Andrew702/4-DOF-Pick-Place-Robot/screen shots/end_scopeout.PNG

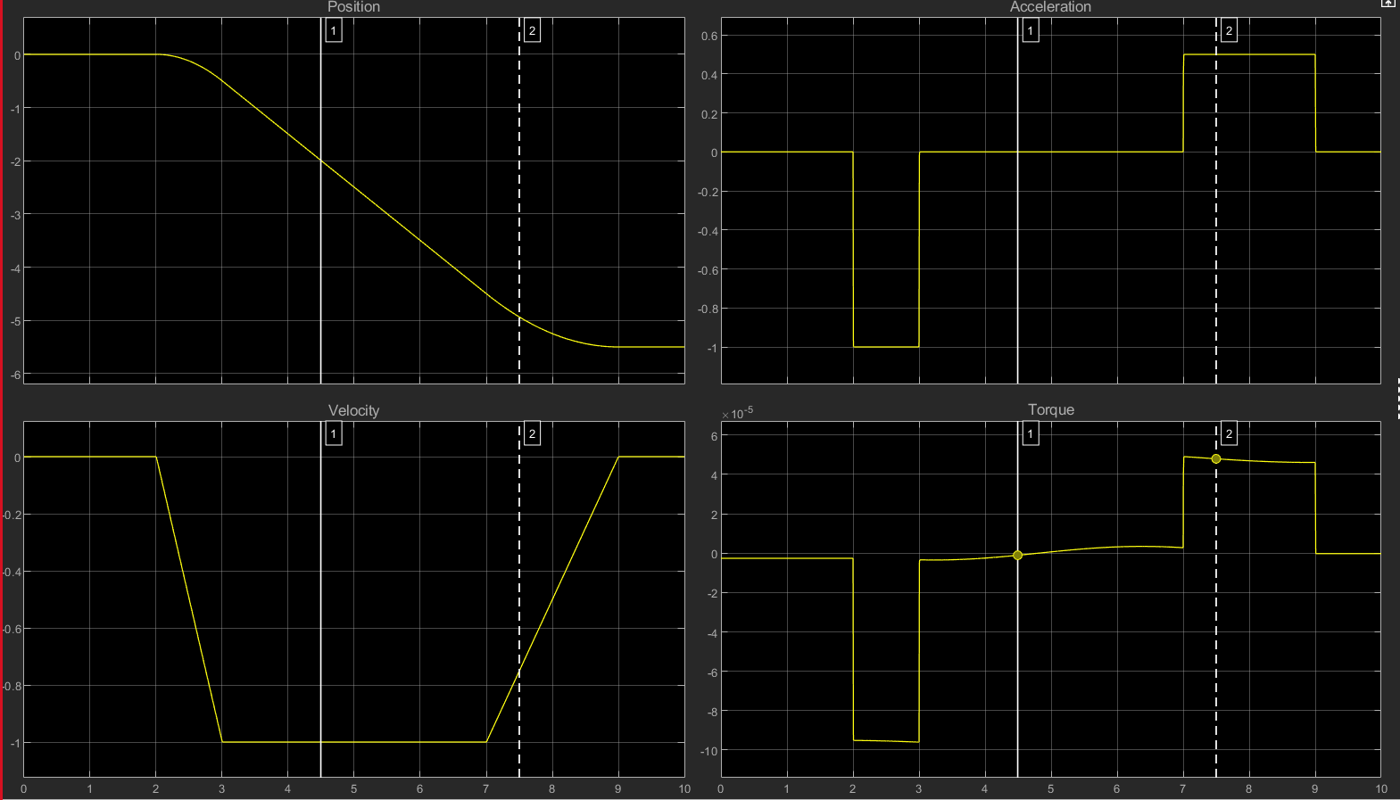
screen shots/end_scopeout.PNG
