Andrew702/4-DOF-Pick-Place-Robot/screen shots/end_torque.PNG

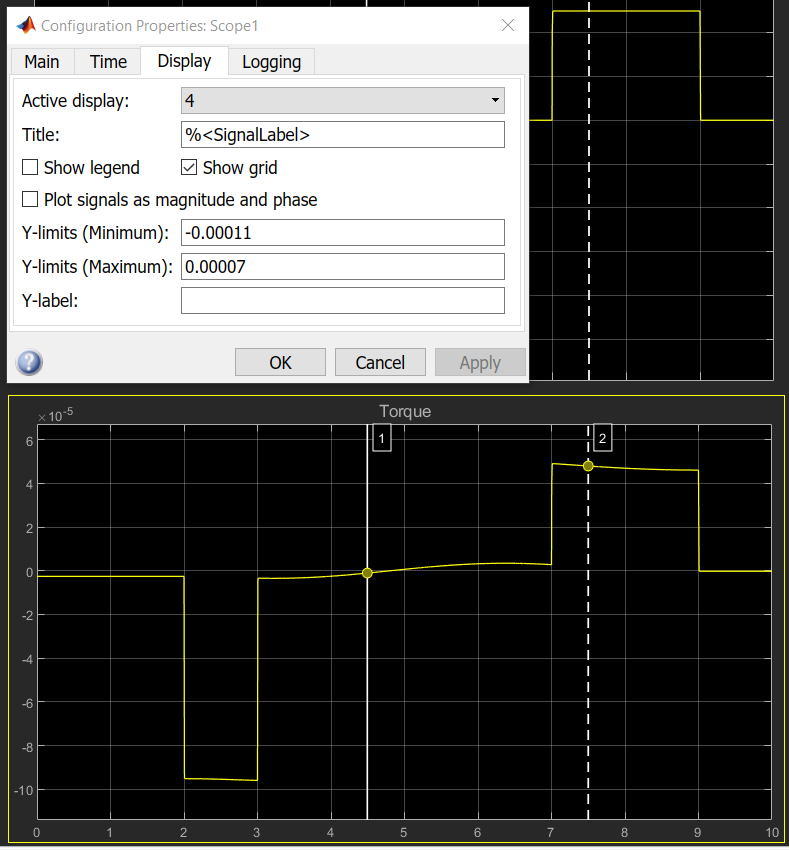
screen shots/end_torque.PNG
