Andrew702/4-DOF-Pick-Place-Robot/screen shots/hm_torque.PNG

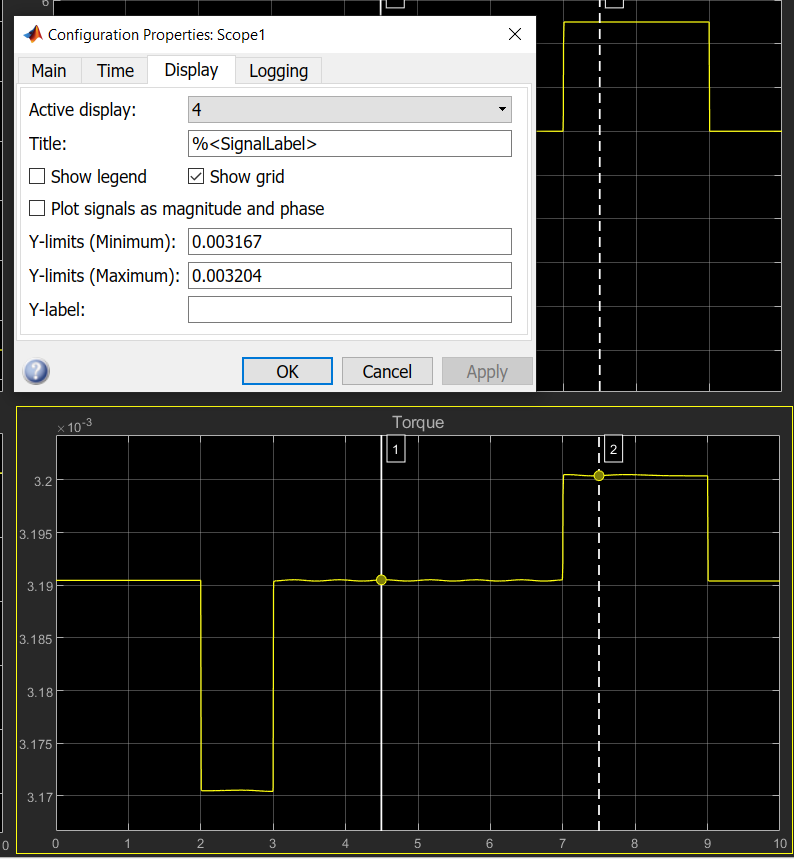
screen shots/hm_torque.PNG
