Andrew702/4-DOF-Pick-Place-Robot/screen shots/pid0.1.PNG

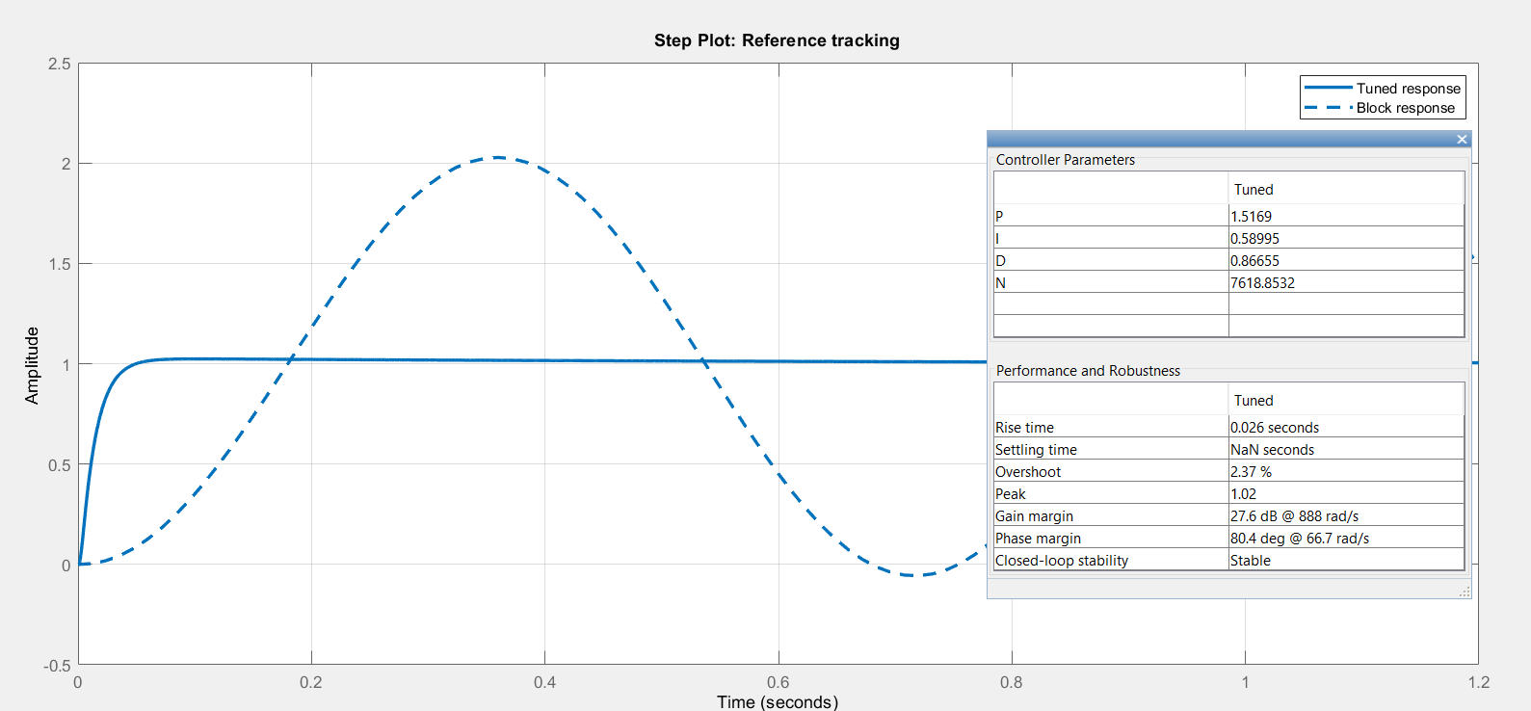
screen shots/pid0.1.PNG
