Andrew702/4-DOF-Pick-Place-Robot/screen shots/pid0.2.PNG

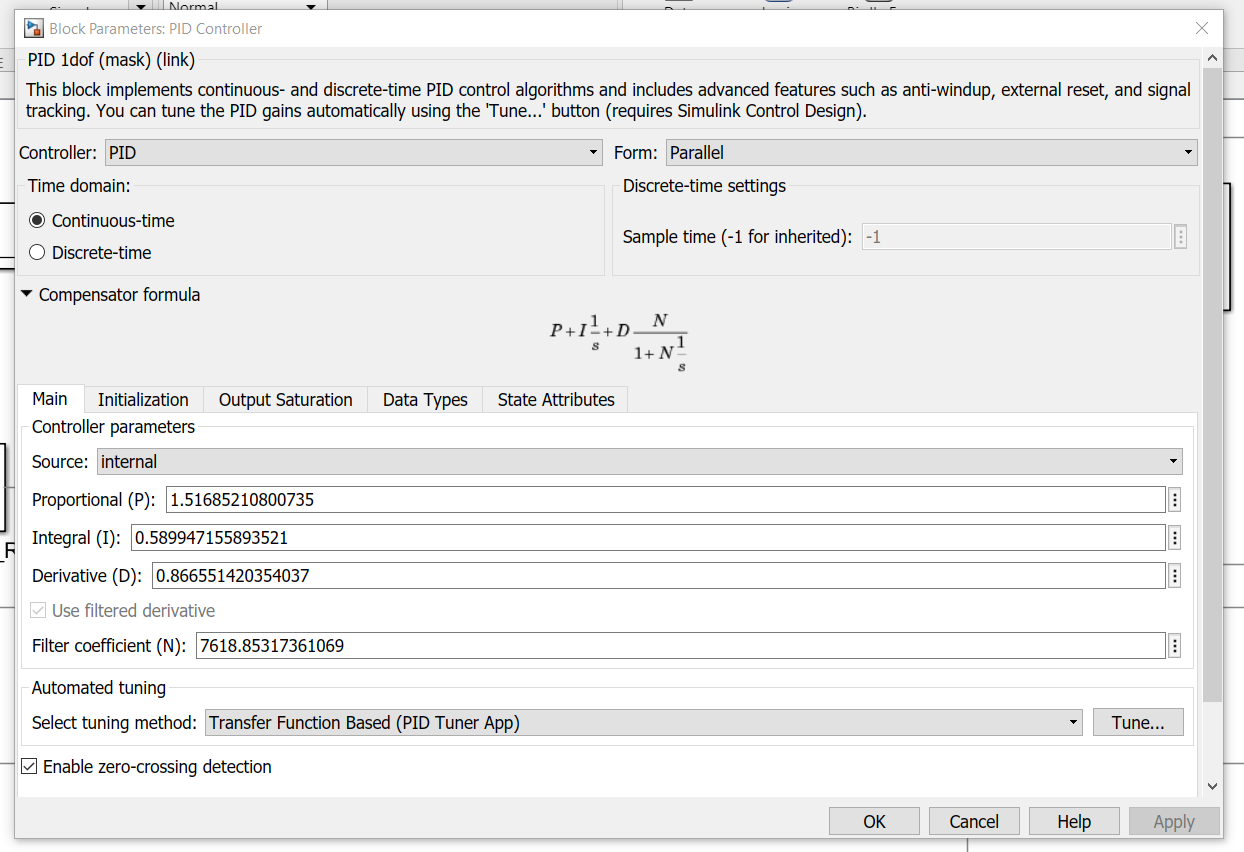
screen shots/pid0.2.PNG
