Andrew702/4-DOF-Pick-Place-Robot/screen shots/pid final.PNG

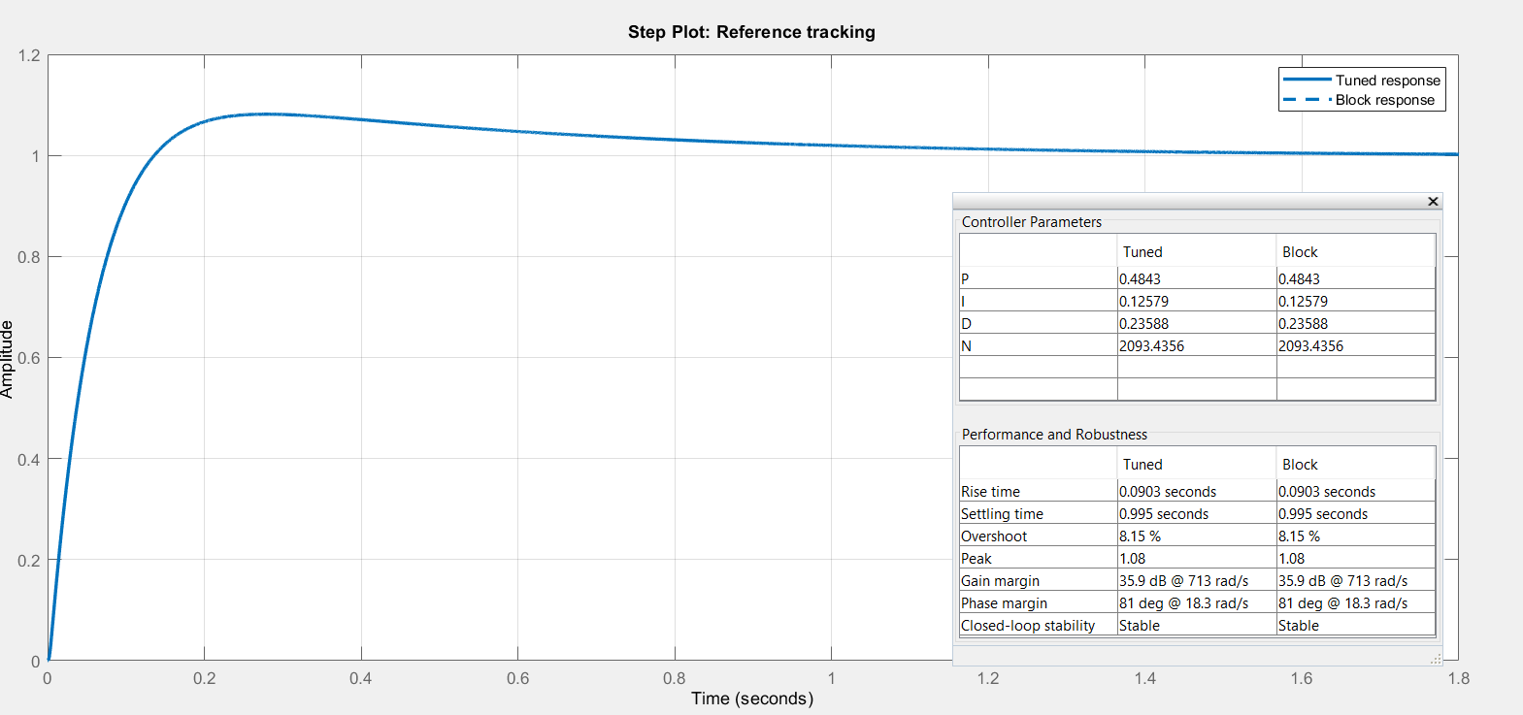
screen shots/pid final.PNG
