Andrew702/4-DOF-Pick-Place-Robot/screen shots/pidsimu.PNG

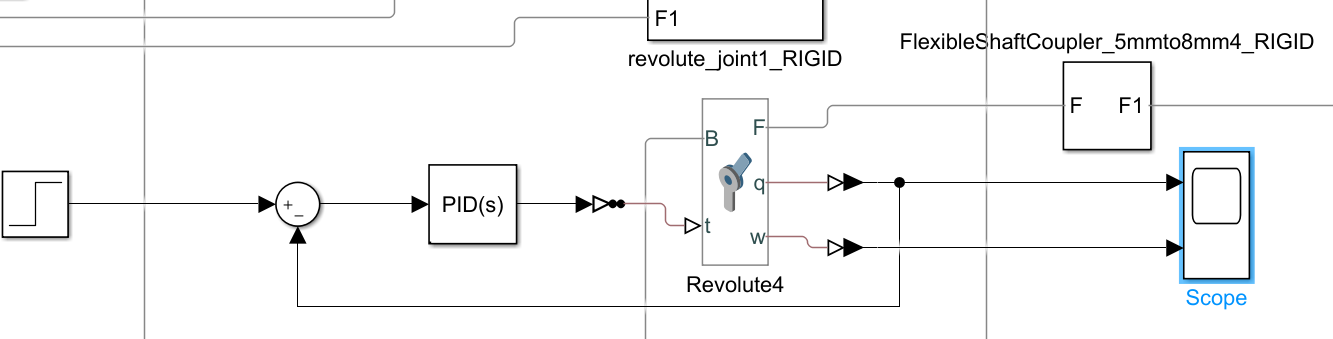
screen shots/pidsimu.PNG
