Andrew702/4-DOF-Pick-Place-Robot/URDF_Config/Capture1.PNG

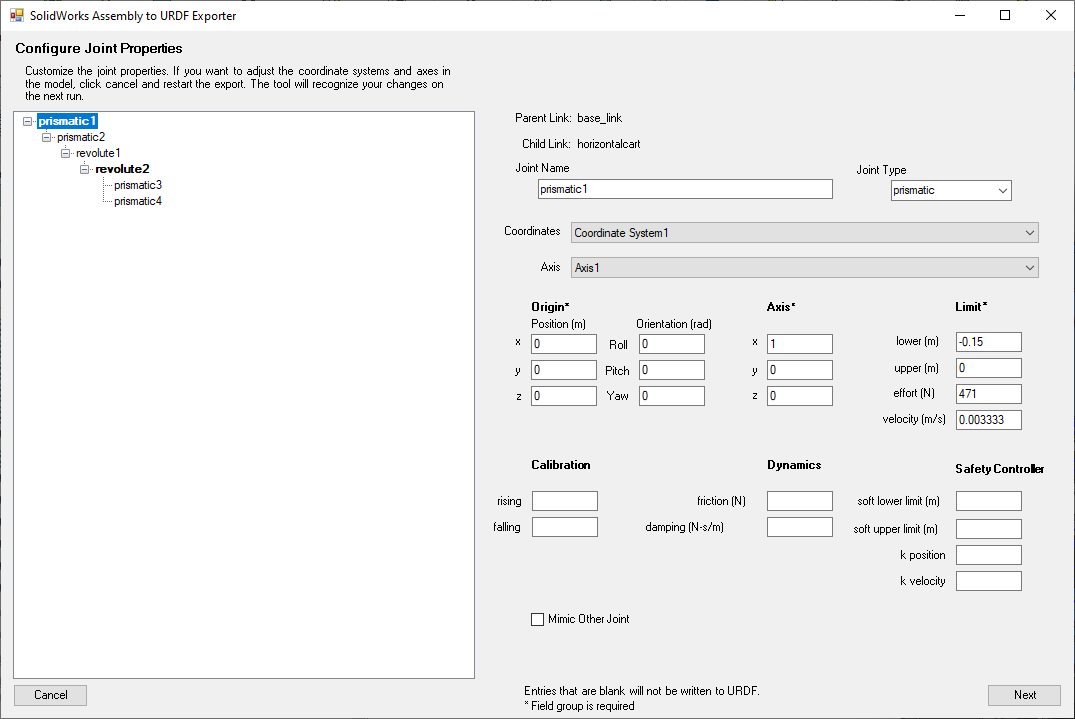
URDF_Config/Capture1.PNG
