Andrew702/4-DOF-Pick-Place-Robot/PCB/pcb230424.sch

## EAGLE design PCB/pcb230424.sch (2025-10-25)

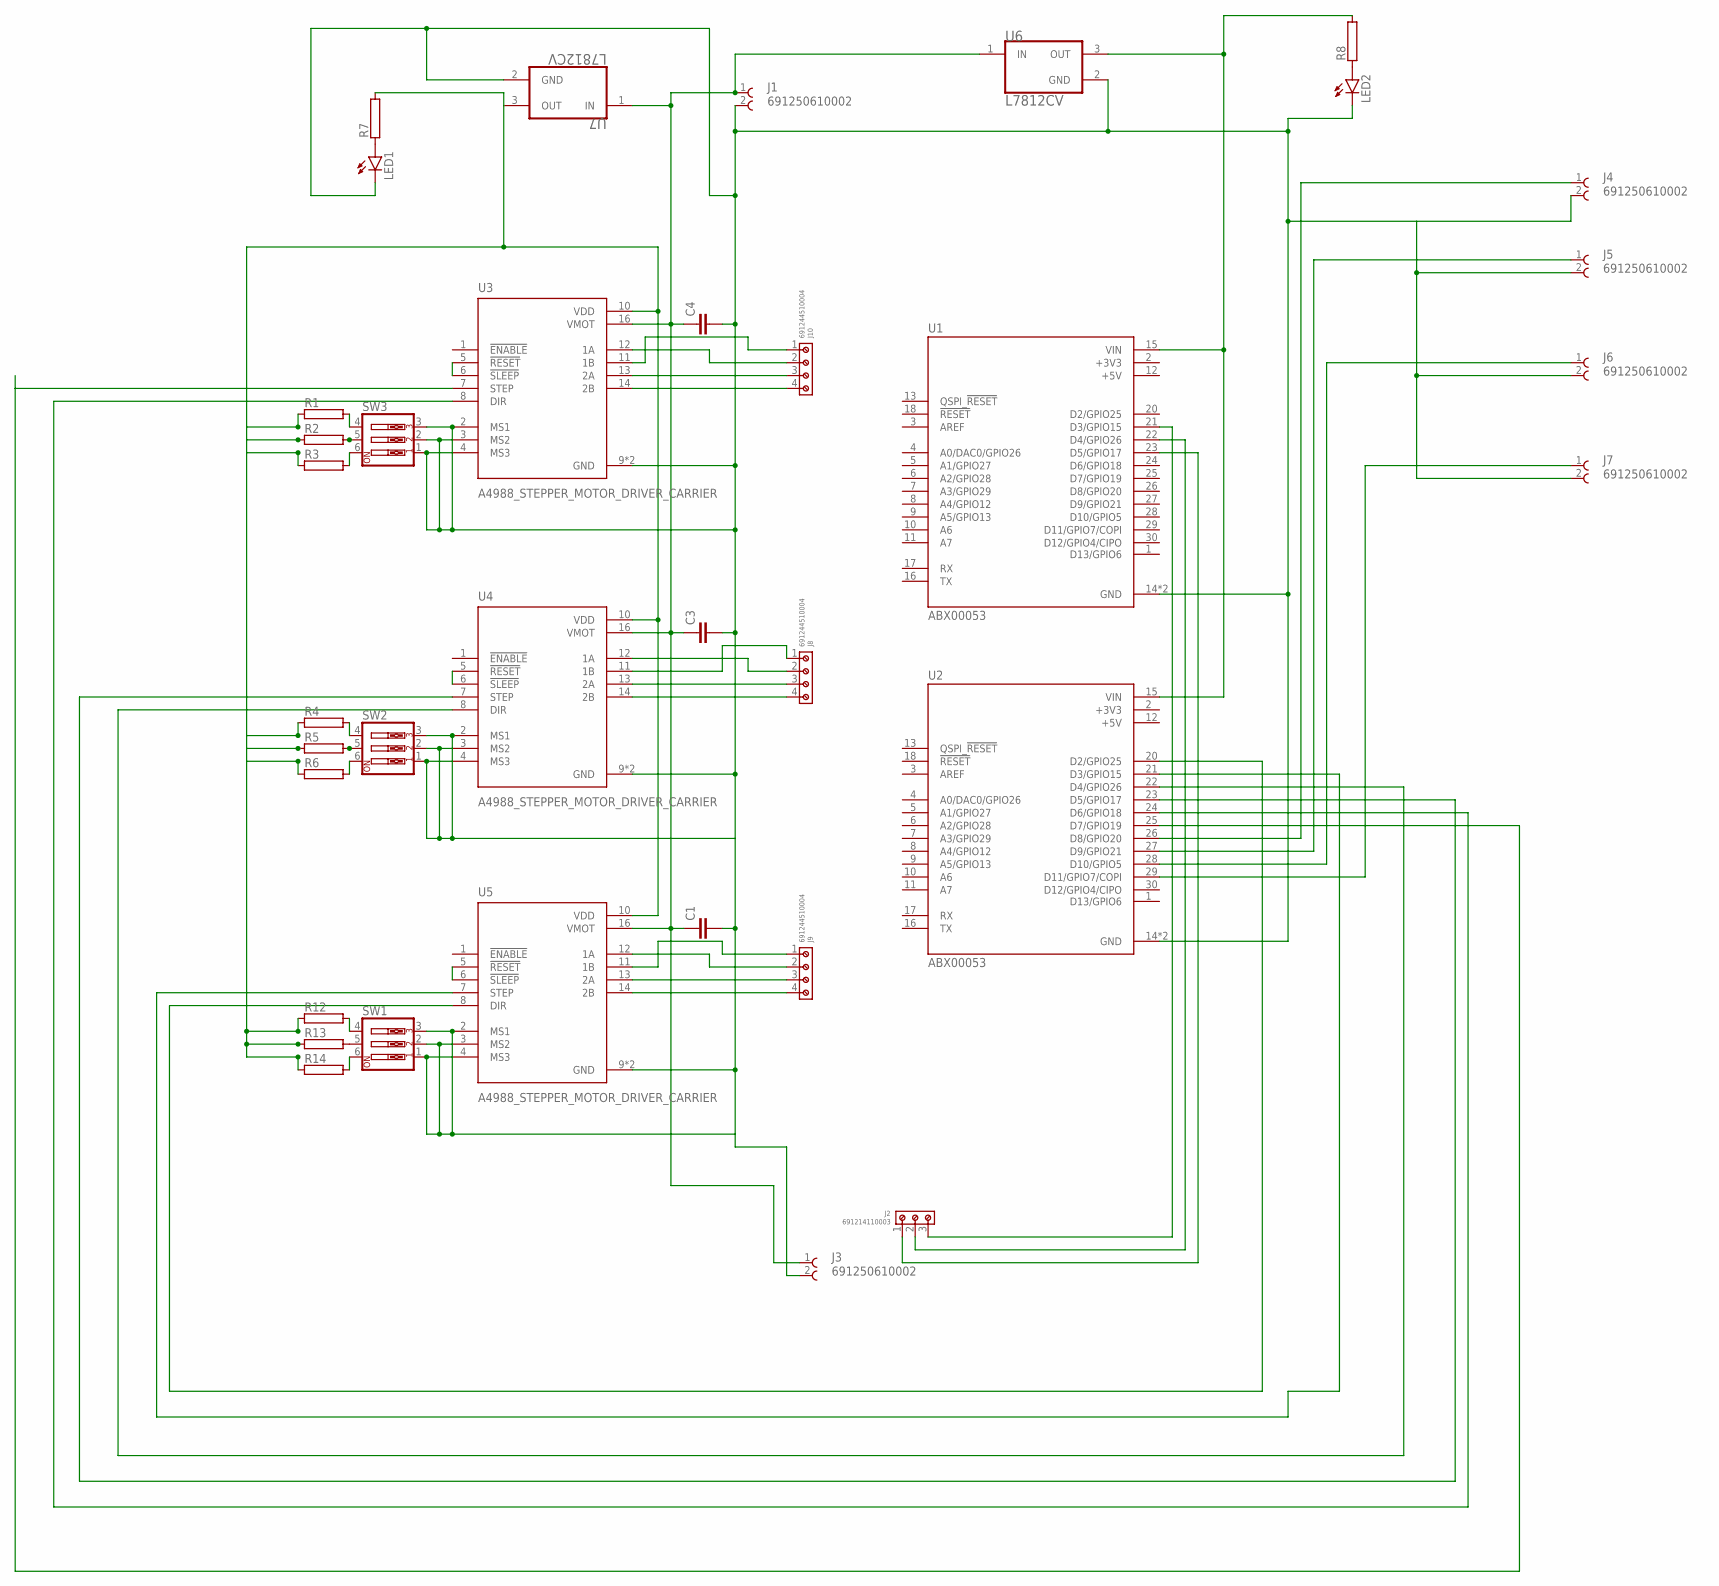
[picture p66: schematic pcb230424.sch]

Parts:
C1, C3, C4: C2,5-3; C2.5-3
J1, J3, J4, J5, J6, J7: 691250610002
J2: 691214110003
J8, J9, J10: 691244510004
LED1, LED2: LED3MM
R1, R2, R3, R4, R5, R6, R7, R8, R12, R13, R14: RAC01; AC01
SW1, SW2, SW3: SW_DIP-3; EDG-03
U1, U2: ABX00053; MODULE_ABX00053
U3, U4, U5: A4988_STEPPER_MOTOR_DRIVER_CARRIER; MODULE_A4988_STEPPER_MOTOR_DRIVER_CARRIER
U6, U7: L7812CV; TO-220-3

Connections:
unnamed: U2.25 (D7/GPIO19), U3.7 (STEP)
unnamed: C1.1, C3.1, C4.1, J1.1, J3.1, U3.16 (VMOT), U4.16 (VMOT), U5.16 (VMOT), U6.1 (IN), U7.1 (IN)
unnamed: R8.2, U1.15 (VIN), U2.15 (VIN), U6.3 (OUT)
unnamed: J10.2, U3.12 (1A)
unnamed: U2.24 (D6/GPIO18), U3.8 (DIR)
unnamed: R13.2, SW1.5
unnamed: J10.3, U3.13 (2A)
unnamed: J10.4, U3.14 (2B)
unnamed: J8.1, U4.11 (1B)
unnamed: J8.2, U4.12 (1A)
unnamed: J8.3, U4.13 (2A)
unnamed: J8.4, U4.14 (2B)
unnamed: J9.2, U5.12 (1A)
unnamed: J9.1, U5.11 (1B)
unnamed: J9.3, U5.13 (2A)
unnamed: J9.4, U5.14 (2B)
unnamed: SW1.1, SW1.2, SW1.3, U5.2 (MS1), U5.3 (MS2), U5.4 (MS3)
unnamed: U2.22 (D4/GPIO26), U4.8 (DIR)
unnamed: U2.23 (D5/GPIO17), U4.7 (STEP)
unnamed: J10.1, U3.11 (1B)
unnamed: R7.2, R12.1, R13.1, R14.1, U3.10 (VDD), U4.10 (VDD), U5.10 (VDD), U7.3 (OUT)
unnamed: U2.20 (D2/GPIO25), U5.8 (DIR)
unnamed: SW2.1, SW2.2, SW2.3, U4.2 (MS1), U4.3 (MS2), U4.4 (MS3)
unnamed: U2.21 (D3/GPIO15), U5.7 (STEP)
unnamed: J4.1, U2.26 (D8/GPIO20)
unnamed: J5.1, U2.27 (D9/GPIO21)
unnamed: J6.1, U2.28 (D10/GPIO5)
unnamed: J7.1, U2.29 (D11/GPIO7/COPI)
unnamed: J2.3, U1.21 (D3/GPIO15)
unnamed: J2.2, U1.22 (D4/GPIO26)
unnamed: J2.1, U1.23 (D5/GPIO17)
unnamed: U3.5 (!RESET), U3.6 (!SLEEP)
unnamed: U4.5 (!RESET), U4.6 (!SLEEP)
unnamed: U5.5 (!RESET), U5.6 (!SLEEP)
unnamed: R12.2, SW1.4
unnamed: C1.2, C3.2, C4.2, J1.2, J3.2, J4.2, J5.2, J6.2, J7.2, LED1.K (C), LED2.K (C), SW3.1, SW3.2, SW3.3, U1.14 (GND), U2.14 (GND), U3.2 (MS1), U3.3 (MS2), U3.4 (MS3), U3.9 (GND), U4.9 (GND), U5.9 (GND), U6.2 (GND), U7.2 (GND)
unnamed: R14.2, SW1.6
unnamed: R4.1, R5.1, R6.1
unnamed: R5.2, SW2.5
unnamed: R4.2, SW2.4
unnamed: R6.2, SW2.6
unnamed: R1.1, R2.1, R3.1
unnamed: R2.2, SW3.5
unnamed: R1.2, SW3.4
unnamed: R3.2, SW3.6
unnamed: LED1.A, R7.1
unnamed: LED2.A, R8.1
